sophiayduan/daydream-sprig/images/sch_peripherals.png

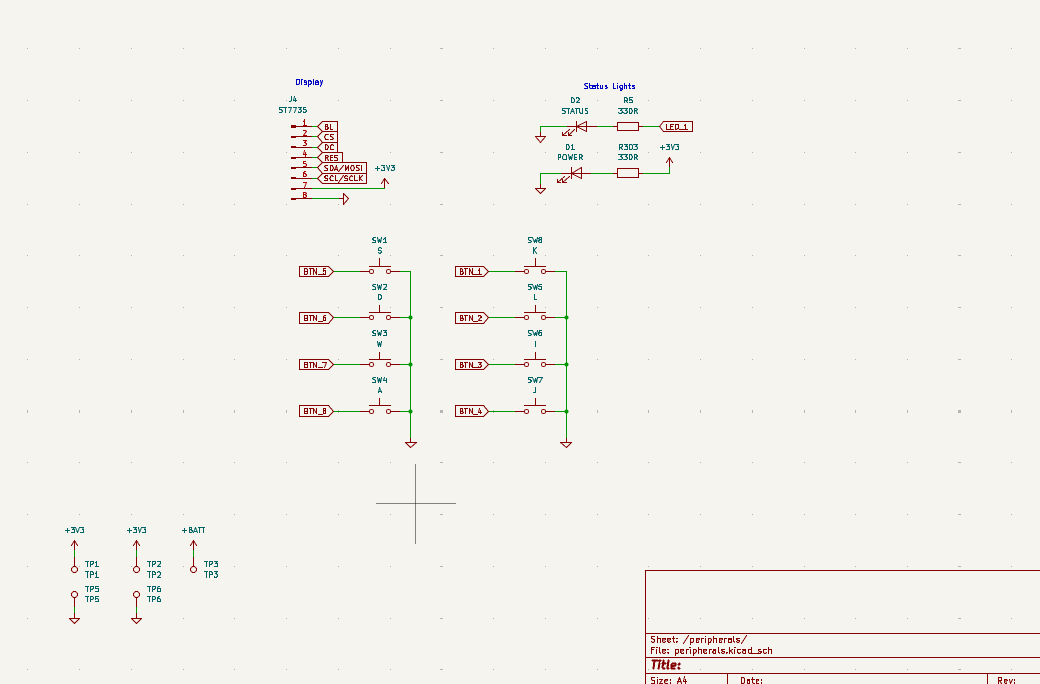
images/sch_peripherals.png
